RBSC/SFG_Clone/Case/sfg_case.jpg

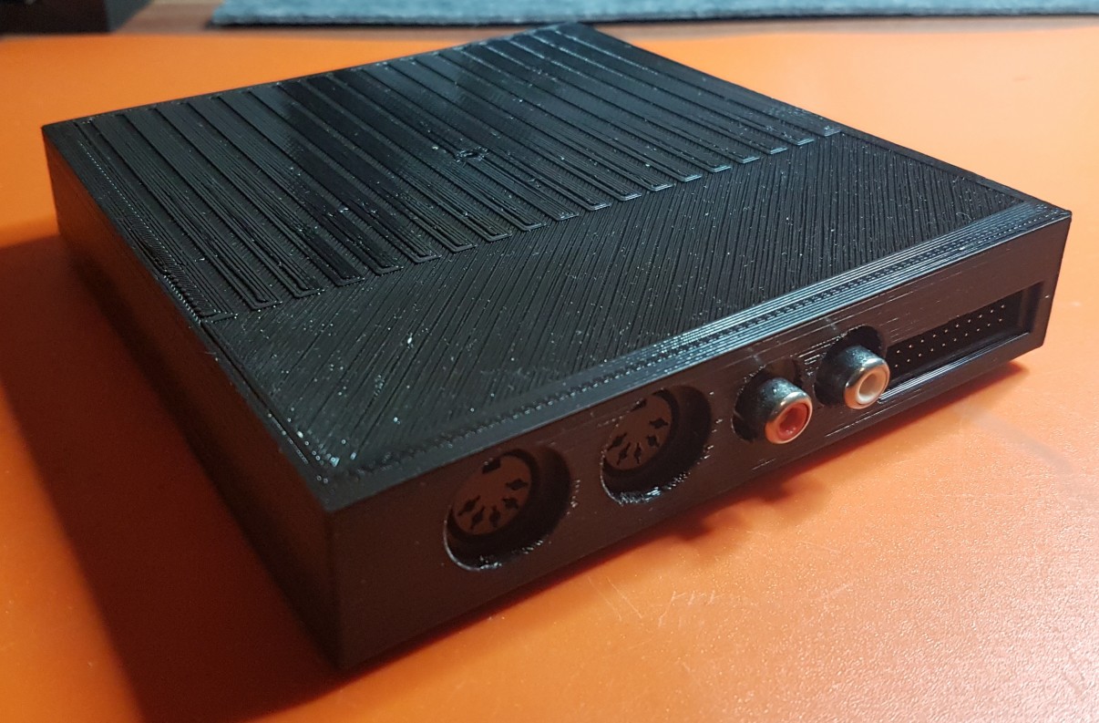
Case/sfg_case.jpg
