RBSC/SFG_Clone/Case/sfg_front_panel.jpg

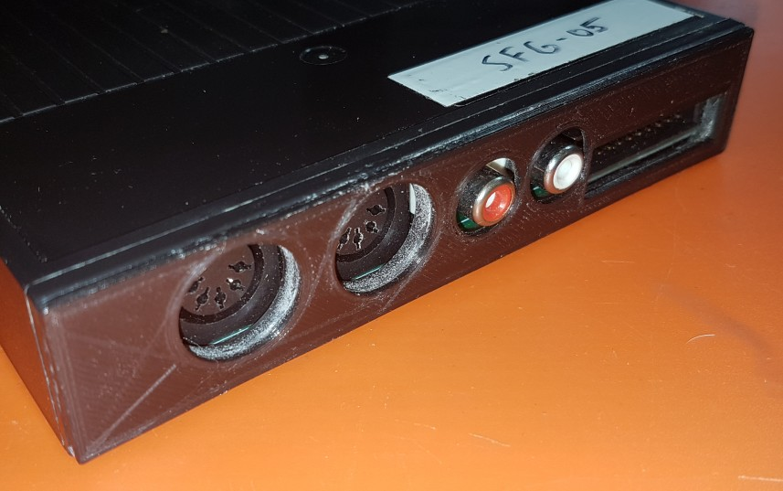
Case/sfg_front_panel.jpg
