RBSC/SFG_Clone/Pics/board.jpg

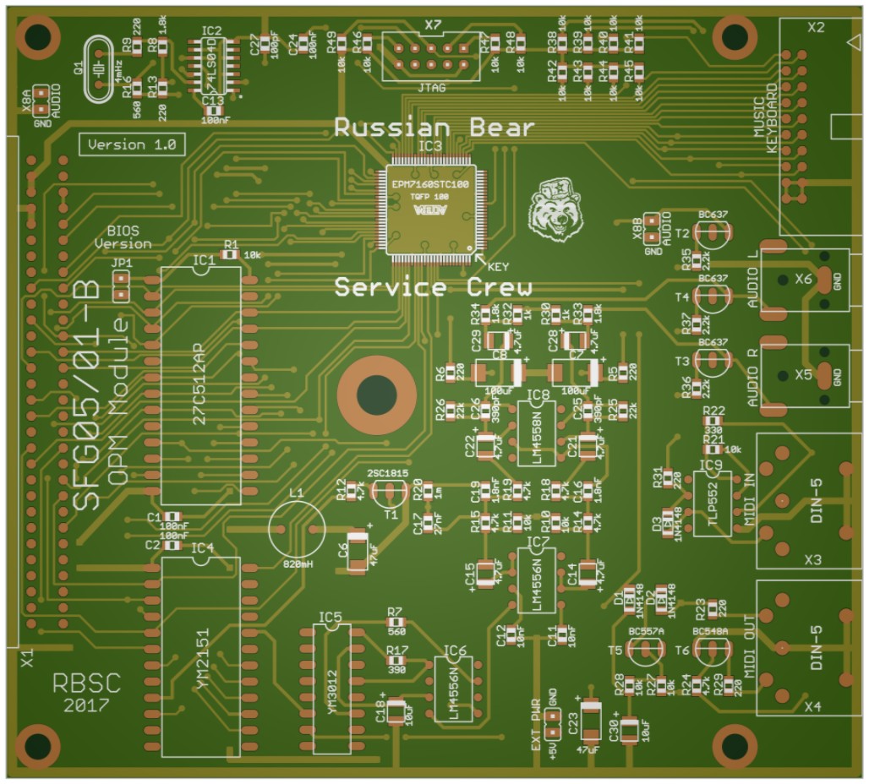
Pics/board.jpg
