RBSC/SFG_Clone/Pics/board_v11.jpg

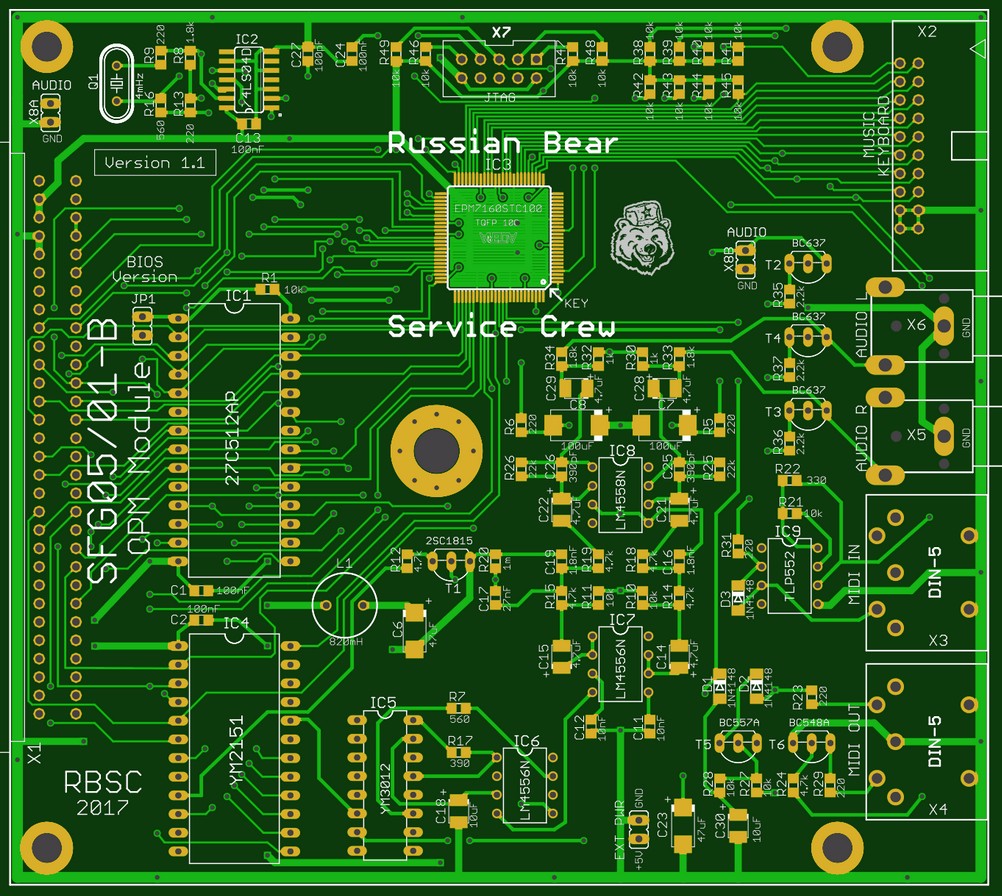
Pics/board_v11.jpg
