RBSC/SFG_Clone/Pics/sfg_case.jpg

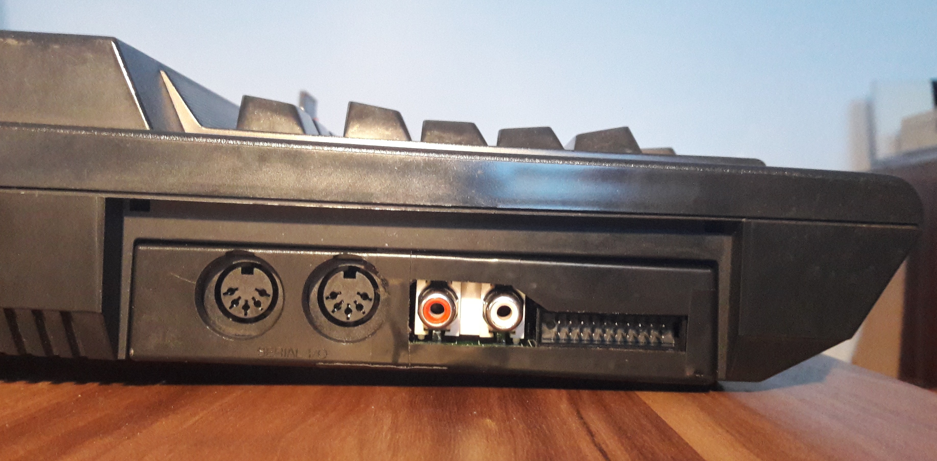
Pics/sfg_case.jpg
