RBSC/SFG_Clone/Pics/assembled_clone.jpg

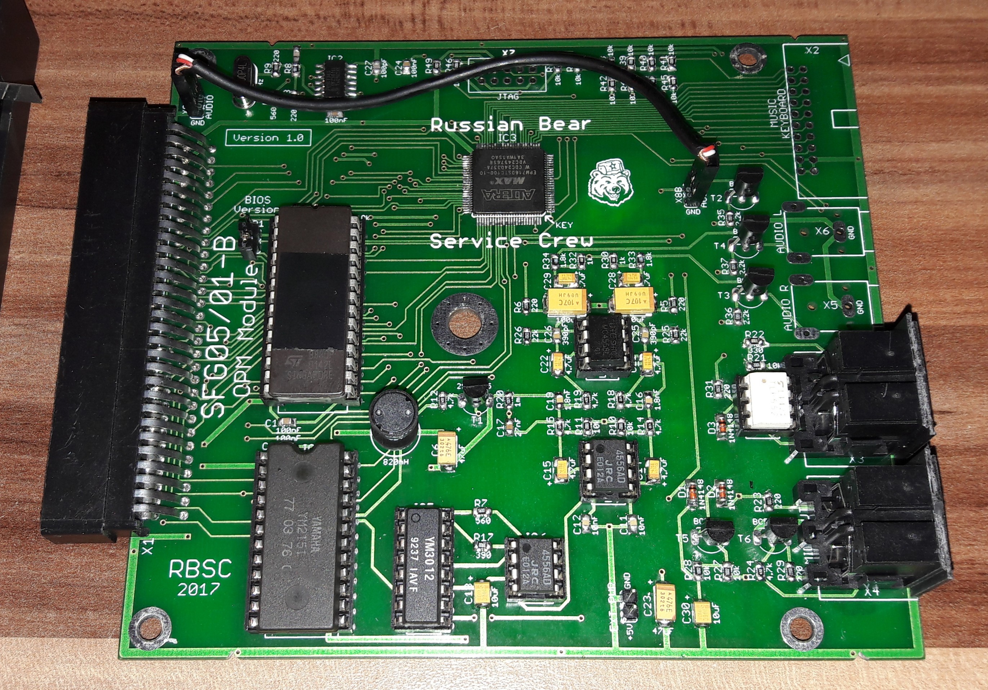
Pics/assembled_clone.jpg
